KawaiiLongmao/alpakka_mod_dual_thumbstick/3d-model/Alpakka单双摇杆文件整理/Alpakka单摇杆[优化3]上壳.stl

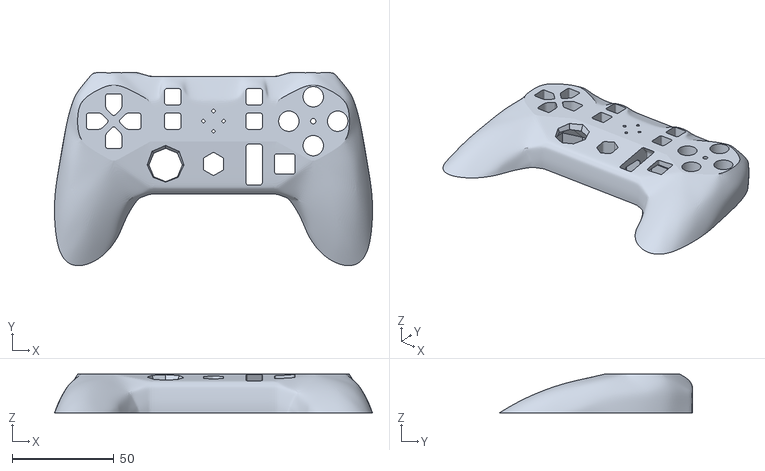
[picture p14: CAD file, 2025-09-16]
3d-model/Alpakka单双摇杆文件整理/Alpakka单摇杆[优化3]上壳.stl
156.2 x 94.9 x 19.0
