KawaiiLongmao/alpakka_mod_dual_thumbstick/3d-model/Alpakka单双摇杆文件整理/剩下的官方文件/secondary_015mm_cover.stl

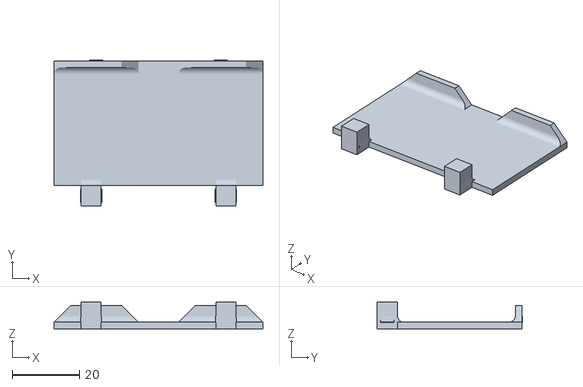
[picture p15: CAD file, 2025-09-16]
3d-model/Alpakka单双摇杆文件整理/剩下的官方文件/secondary_015mm_cover.stl
62.0 x 43.2 x 8.00
