KawaiiLongmao/alpakka_mod_dual_thumbstick/3d-model/Alpakka单双摇杆文件整理/单双摇杆共用/button_abxy.stl

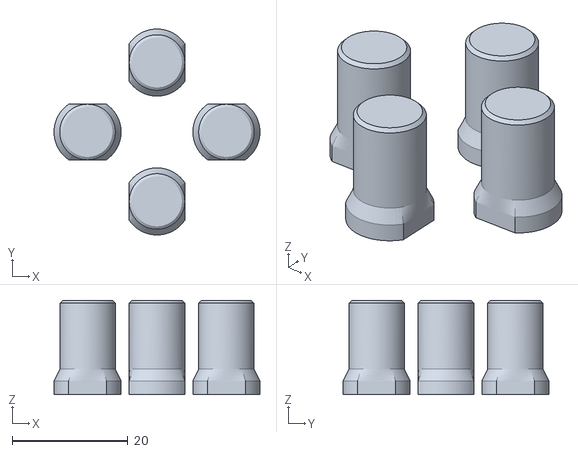
[picture p16: CAD file, 2025-09-16]
3d-model/Alpakka单双摇杆文件整理/单双摇杆共用/button_abxy.stl
35.6 x 35.6 x 16.3
