KawaiiLongmao/alpakka_mod_dual_thumbstick/3d-model/Alpakka单摇杆[优化3][螺丝替代面板]/stl/hexagon.stl

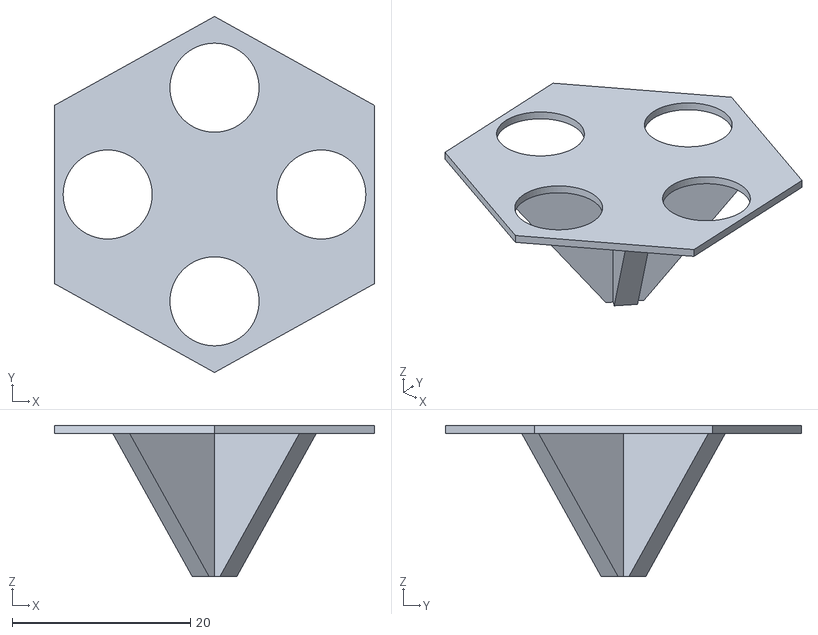
[picture p17: CAD file, 2025-09-16]
3d-model/Alpakka单摇杆[优化3][螺丝替代面板]/stl/hexagon.stl
36.0 x 40.0 x 17.0
