KawaiiLongmao/alpakka_mod_dual_thumbstick/3d-model/Alpakka双摇杆[1.1.4][平整面壳]/stl/button_dpad.stl

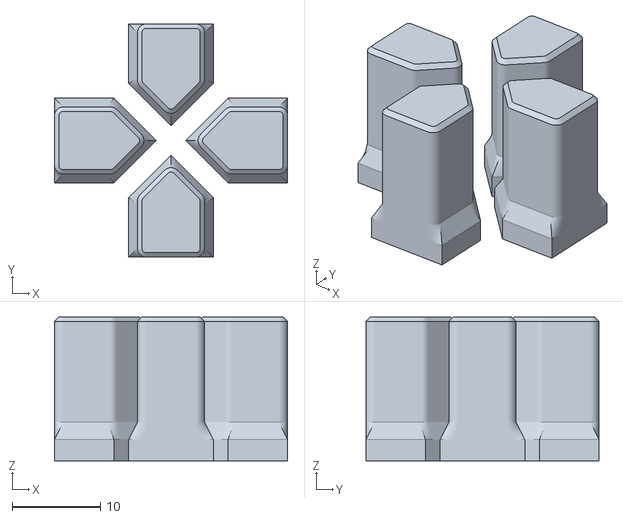
[picture p18: CAD file, 2025-09-16]
3d-model/Alpakka双摇杆[1.1.4][平整面壳]/stl/button_dpad.stl
26.4 x 26.4 x 16.3
