KawaiiLongmao/alpakka_mod_dual_thumbstick/3d-model/Alpakka单双摇杆文件整理/Alpakka单摇杆home键.stl

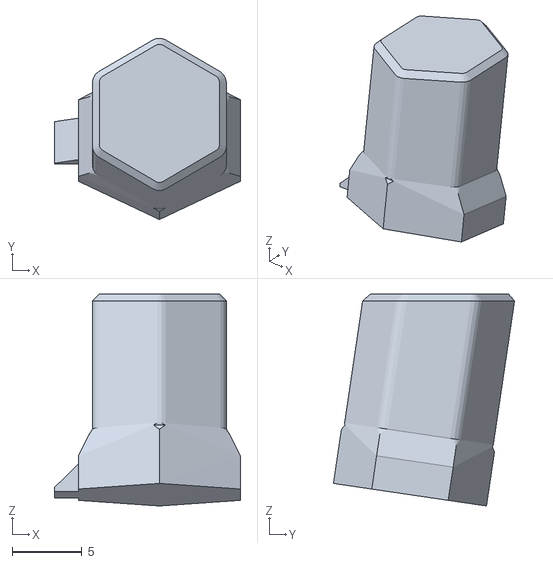
[picture p19: CAD file, 2025-09-16]
3d-model/Alpakka单双摇杆文件整理/Alpakka单摇杆home键.stl
13.3 x 12.9 x 15.2
