KawaiiLongmao/alpakka_mod_dual_thumbstick/3d-model/Alpakka单双摇杆文件整理/剩下的官方文件/primary_015mm_trigger_L2.stl

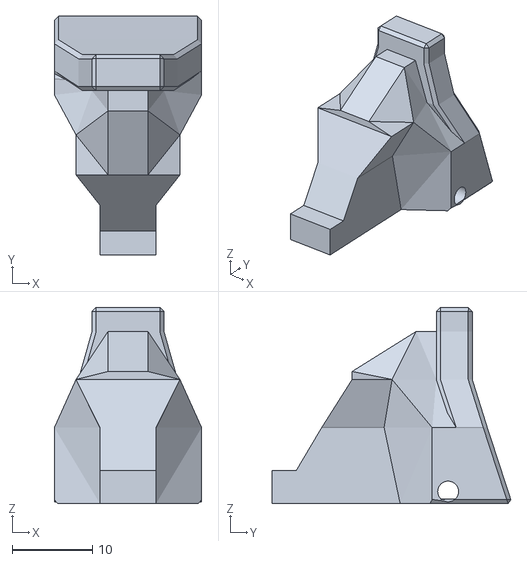
[picture p20: CAD file, 2025-09-16]
3d-model/Alpakka单双摇杆文件整理/剩下的官方文件/primary_015mm_trigger_L2.stl
18.4 x 29.8 x 24.5
