KawaiiLongmao/alpakka_mod_dual_thumbstick/3d-model/Alpakka单双摇杆文件整理/剩下的官方文件/secondary_015mm_wheel.stl

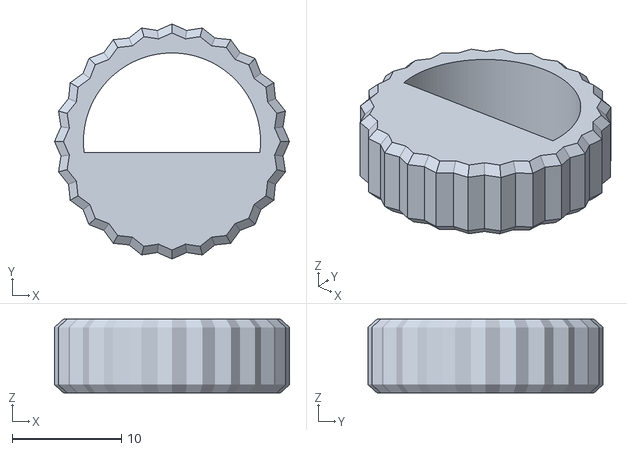
[picture p21: CAD file, 2025-09-16]
3d-model/Alpakka单双摇杆文件整理/剩下的官方文件/secondary_015mm_wheel.stl
21.5 x 21.5 x 6.75
