KawaiiLongmao/alpakka_mod_dual_thumbstick/3d-model/Alpakka单双摇杆文件整理/剩下的官方文件/primary_015mm_trigger_L1.stl

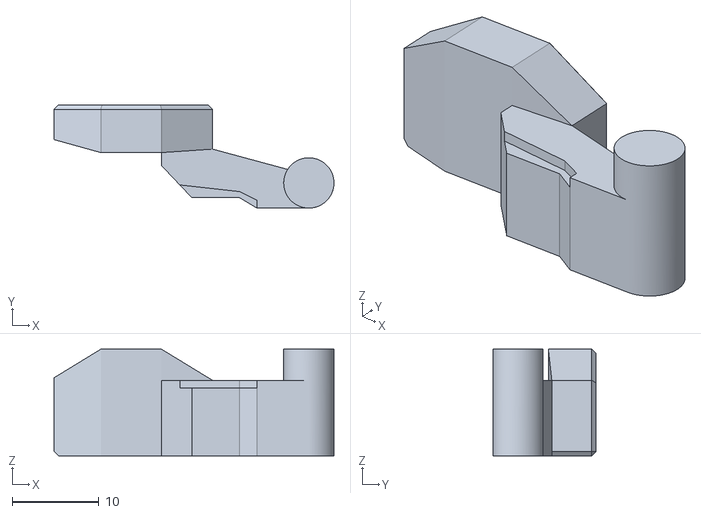
[picture p22: CAD file, 2025-09-16]
3d-model/Alpakka单双摇杆文件整理/剩下的官方文件/primary_015mm_trigger_L1.stl
32.3 x 11.9 x 12.3
