KawaiiLongmao/alpakka_mod_dual_thumbstick/3d-model/Alpakka单双摇杆文件整理/剩下的官方文件/secondary_007mm_wheel_core.stl

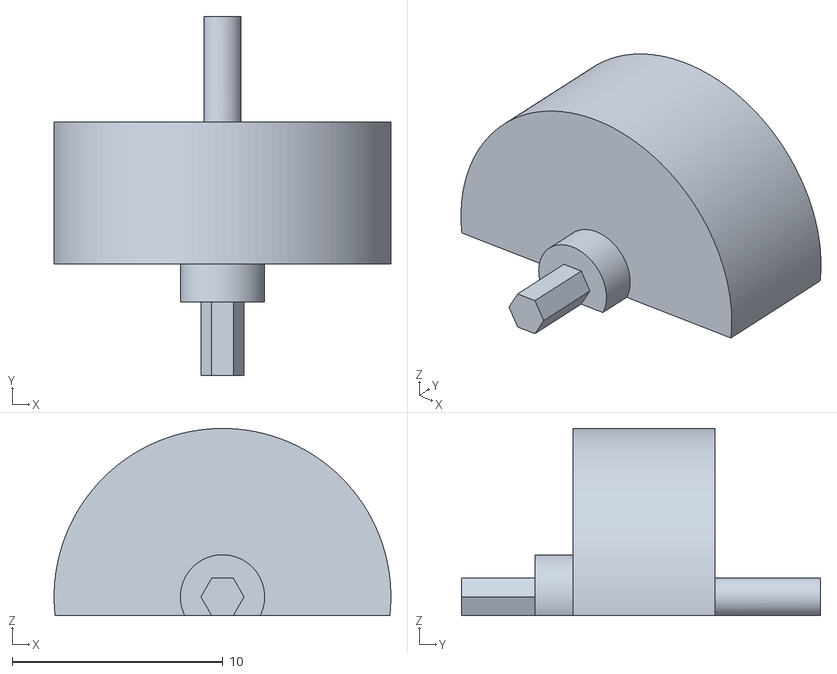
[picture p23: CAD file, 2025-09-16]
3d-model/Alpakka单双摇杆文件整理/剩下的官方文件/secondary_007mm_wheel_core.stl
16.0 x 17.1 x 8.89
