KawaiiLongmao/alpakka_mod_dual_thumbstick/3d-model/Alpakka单双摇杆文件整理/剩下的官方文件/primary_007mm_select_4x.stl

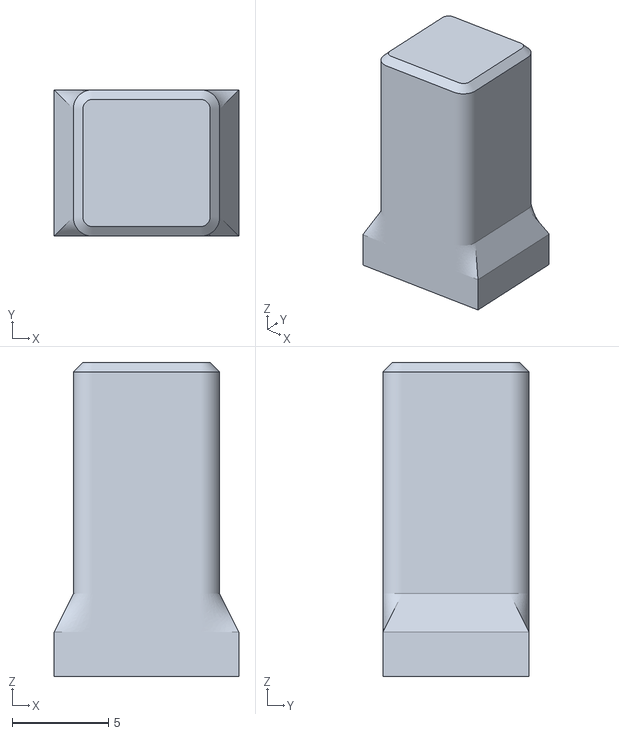
[picture p24: CAD file, 2025-09-16]
3d-model/Alpakka单双摇杆文件整理/剩下的官方文件/primary_007mm_select_4x.stl
9.60 x 7.60 x 16.3
