KawaiiLongmao/alpakka_mod_dual_thumbstick/3d-model/Alpakka单双摇杆文件整理/剩下的官方文件/any_015mm_wheel_holder.stl

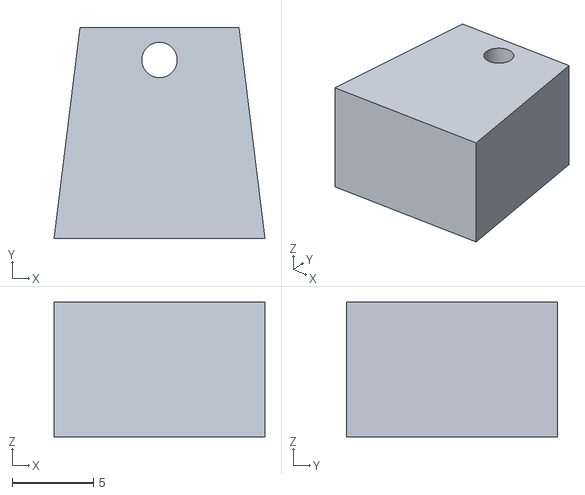
[picture p25: CAD file, 2025-09-16]
3d-model/Alpakka单双摇杆文件整理/剩下的官方文件/any_015mm_wheel_holder.stl
13.0 x 13.0 x 8.30
